FelixMarian/SRA_Temperatura/src/SRA_temp/set_param.h

#ifndef SET_PARAM_H
#define SET_PARAM_H

set_param(int menuState){
  switch (menuState) {
      case 0:
        break;
      case 1:
        break;
      case 2:
        break;
      case 3:
        break;
      case 4:
        break;
      case 5:
        break;
      case 6:
        break;
      case 7:
        break;
    }
}

void showValue(){
  
}

#endif
